dizcza/flashlight_kicad/images/bullet-hole/ai1.jpeg

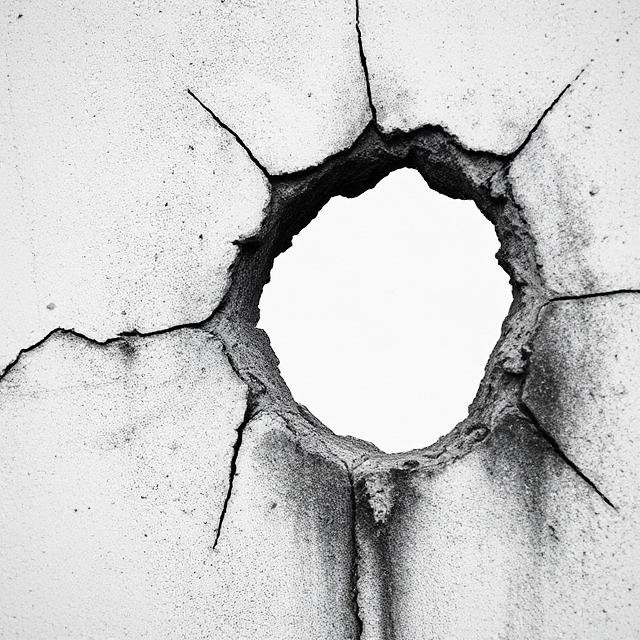
images/bullet-hole/ai1.jpeg
