dizcza/flashlight_kicad/images/bullet-hole/collection.jpg

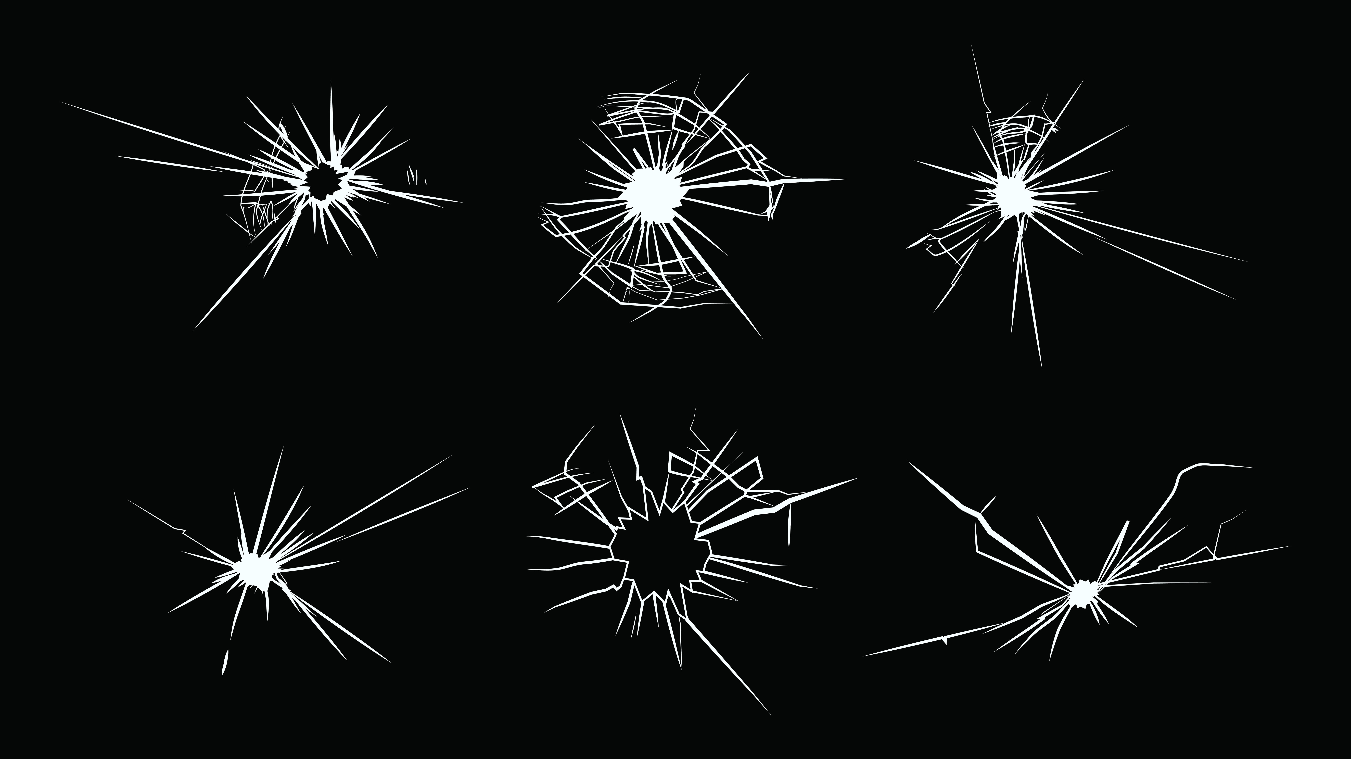
images/bullet-hole/collection.jpg
