dizcza/flashlight_kicad/images/bullet-hole/patch4.png

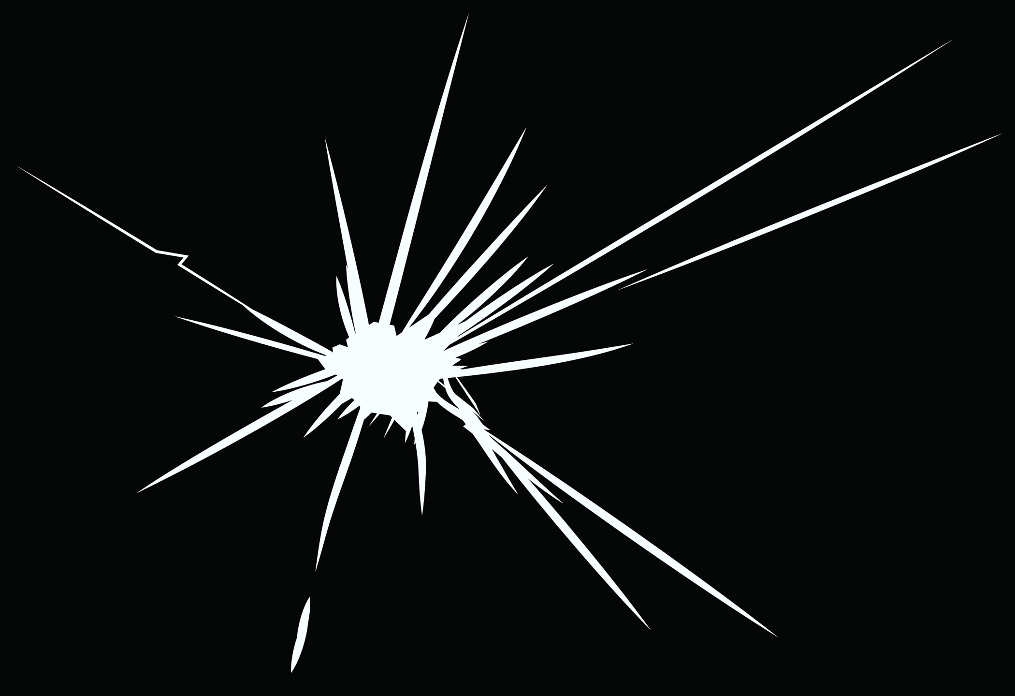
images/bullet-hole/patch4.png
